vpatkov/esr-meter/ltspice/peak-detector.asc

C1: cap; 1n
C2: cap; 10n
C3: cap; 100n
D1: diode; BAS16HY
D2: diode; BAS16HY
R1: res; 10k
R2: res; 1k
R3: res; 100Meg
R4: res; 3.3Meg
R5: res; 100k
U1: opamp2; OPA1678
U2: opamp2; OPA1678
V1: voltage; {vcc}; Rser=0.1
V2: voltage; {-vcc}; Rser=0.1
V3: voltage; SINE(0 {in} 100k)
Named nets: 0, VCC, VEE, OUT
.tran 5m
.param vcc=3.3
.step dec param in 0.01 1 5
.meas out AVG V(OUT) FROM 4m
.meas TRAN ratio PARAM out/in
.lib opa1678.lib
