vpatkov/esr-meter/ltspice/wien.asc

C1: cap; 1n
C2: cap; 1n
C3: cap; 10n
C6: cap; 10n
D1: diode; BAS16HY
D2: diode; BAS16HY
J1: njf; J113
R1: res; 2.2k
R2: res; 1k
R3: res; 1.58k
R4: res; 1.58k
R5: res; 300
R6: res; 10k
R7: res; 499
R8: res; 10
R9: res; 1k
R10: res; 100k
R11: res; 1k
U1: opamp2; OPA1678
U2: opamp2; OPA1678
V1: voltage; {vcc}; Rser=0.1
V2: voltage; {-vcc}; Rser=0.1
V3: voltage; 1.24
Named nets: 0, VCC, VEE, AGC, OUT
.tran 5m uic
.param vcc=3.3
.lib opa1678.lib
